Lithopop/OpenSlab/Gallery/IMG20250224133005.jpg

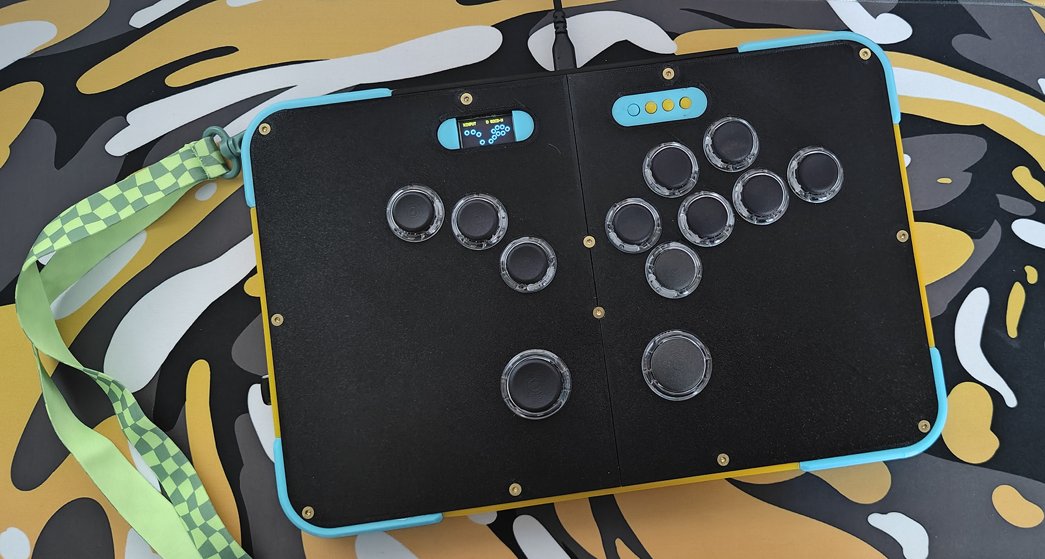
Gallery/IMG20250224133005.jpg
