Lithopop/OpenSlab/Print-Build Files/- Frame Common Files/bottom wall.stl

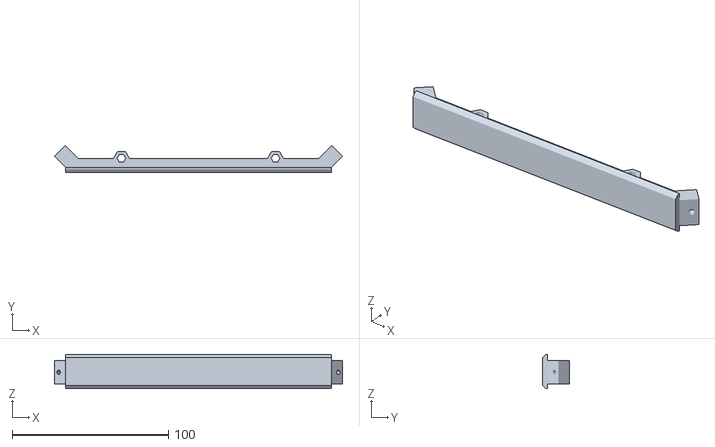
[picture p14: CAD file, 2025-02-19]
Print-Build Files/- Frame Common Files/bottom wall.stl
184.3 x 17.0 x 22.0
