Lithopop/OpenSlab/Print-Build Files/! Experimental/Acrylic Steel Plates ERGOd/Screen holder.stl

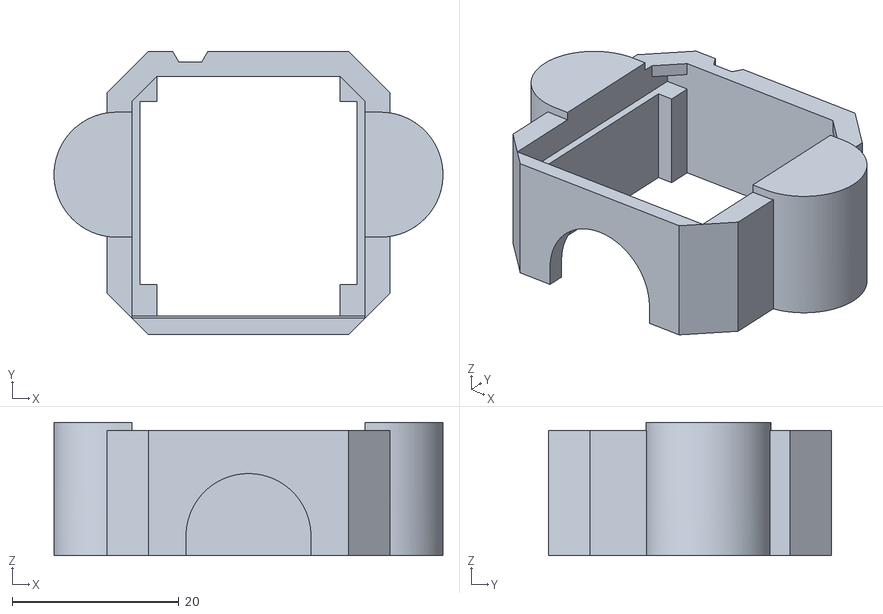
[picture p15: CAD file, 2025-02-19]
Print-Build Files/! Experimental/Acrylic Steel Plates ERGOd/Screen holder.stl
46.7 x 34.0 x 16.0
