Lithopop/OpenSlab/Print-Build Files/! Experimental/Acrylic Steel Plates ERGOd/bottom plexi.stl

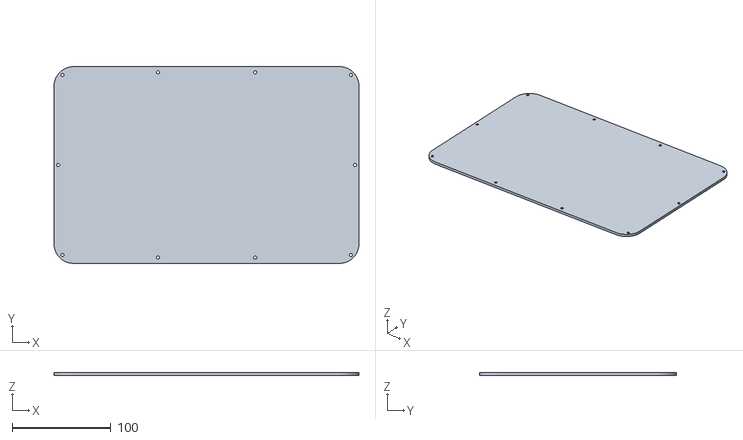
[picture p16: CAD file, 2025-02-19]
Print-Build Files/! Experimental/Acrylic Steel Plates ERGOd/bottom plexi.stl
309.4 x 199.6 x 3.00
