Lithopop/OpenSlab/Print-Build Files/- 3D Print Plates Common Files/button round 3d print.stl

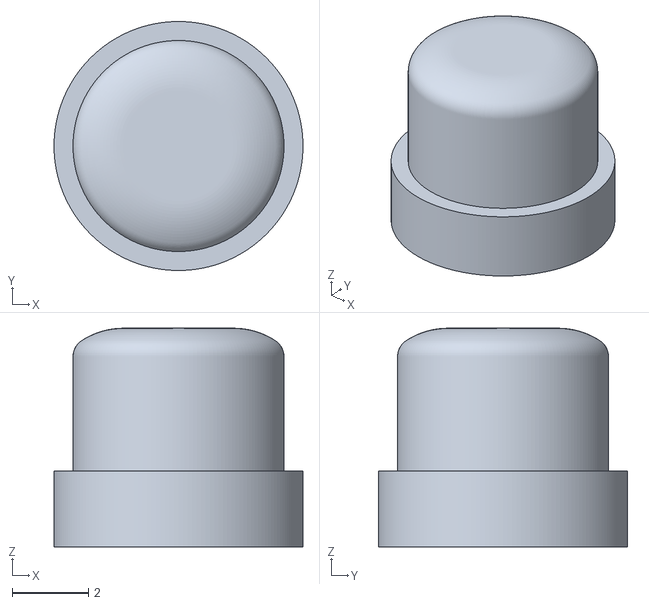
[picture p17: CAD file, 2025-02-19]
Print-Build Files/- 3D Print Plates Common Files/button round 3d print.stl
6.55 x 6.55 x 5.75
