Lithopop/OpenSlab/Print-Build Files/- Frame Common Files/Top Left.stl

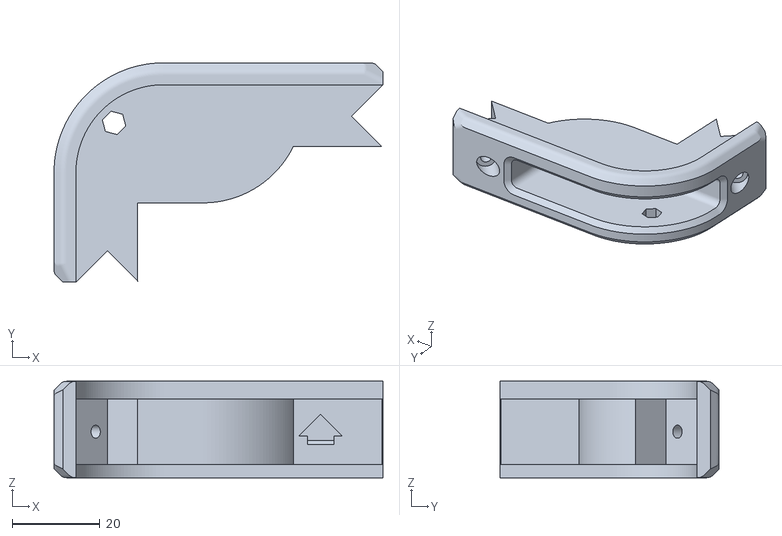
[picture p18: CAD file, 2025-02-19]
Print-Build Files/- Frame Common Files/Top Left.stl
75.0 x 50.0 x 22.0
