Lithopop/OpenSlab/Print-Build Files/! Experimental/Acrylic Steel Plates ERGOd/Steel Top.stl

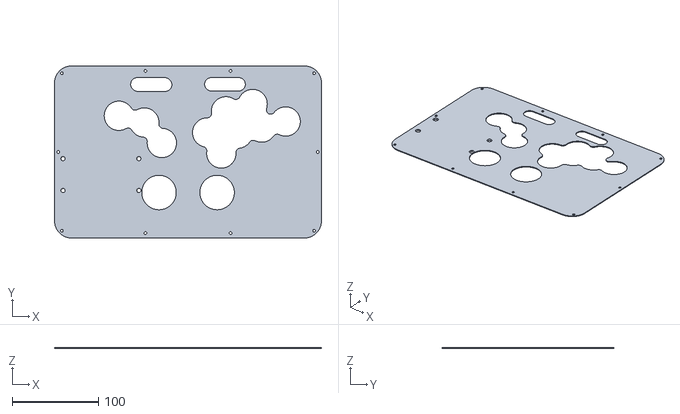
[picture p19: CAD file, 2025-02-19]
Print-Build Files/! Experimental/Acrylic Steel Plates ERGOd/Steel Top.stl
309.6 x 199.6 x 1.00
