Lithopop/OpenSlab/Print-Build Files/- 3D Print Plates Common Files/aux frame bottom.stl

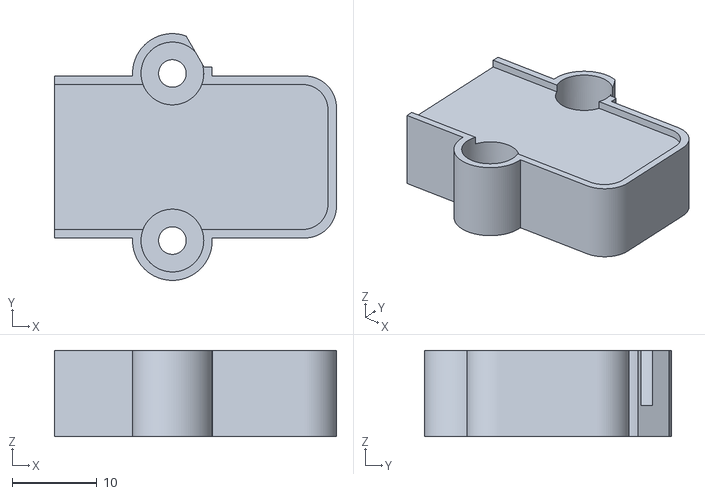
[picture p20: CAD file, 2025-02-19]
Print-Build Files/- 3D Print Plates Common Files/aux frame bottom.stl
33.2 x 29.1 x 10.2
