Lithopop/OpenSlab/Print-Build Files/! Experimental/Acrylic Steel Plates ERGOd/aux frame bottom plexi.stl

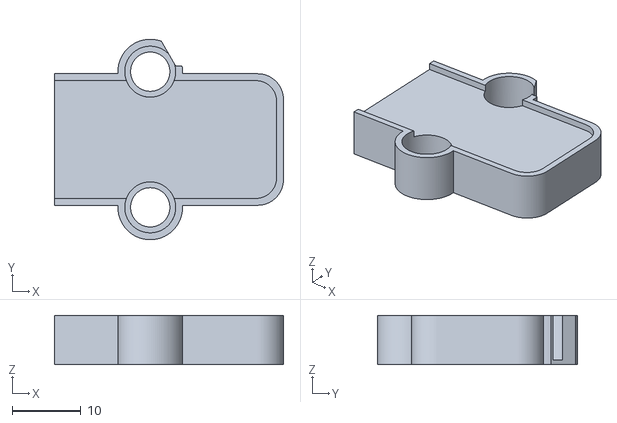
[picture p21: CAD file, 2025-02-19]
Print-Build Files/! Experimental/Acrylic Steel Plates ERGOd/aux frame bottom plexi.stl
33.2 x 29.1 x 7.15
