Lithopop/OpenSlab/Print-Build Files/- 3D Print Plates Common Files/Screen holder.stl

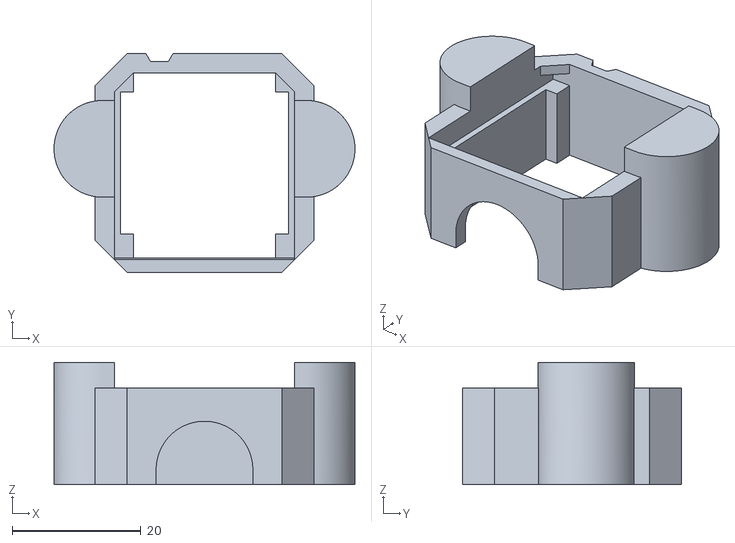
[picture p22: CAD file, 2025-02-19]
Print-Build Files/- 3D Print Plates Common Files/Screen holder.stl
46.7 x 34.0 x 19.0
