Lithopop/OpenSlab/Print-Build Files/- Frame Common Files/RP mount lid.stl

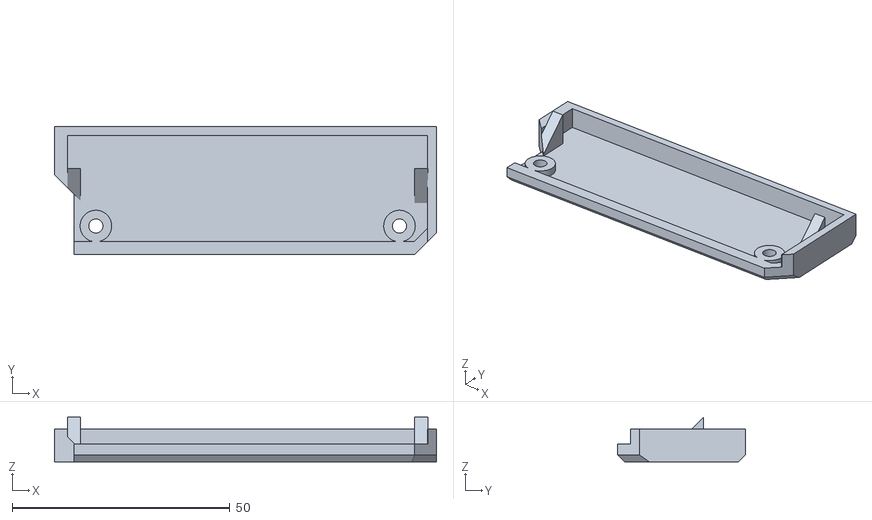
[picture p23: CAD file, 2025-02-19]
Print-Build Files/- Frame Common Files/RP mount lid.stl
87.7 x 29.3 x 10.2
