Lithopop/OpenSlab/Print-Build Files/! Experimental/Acrylic Steel Plates ERGOd/plexi Top.stl

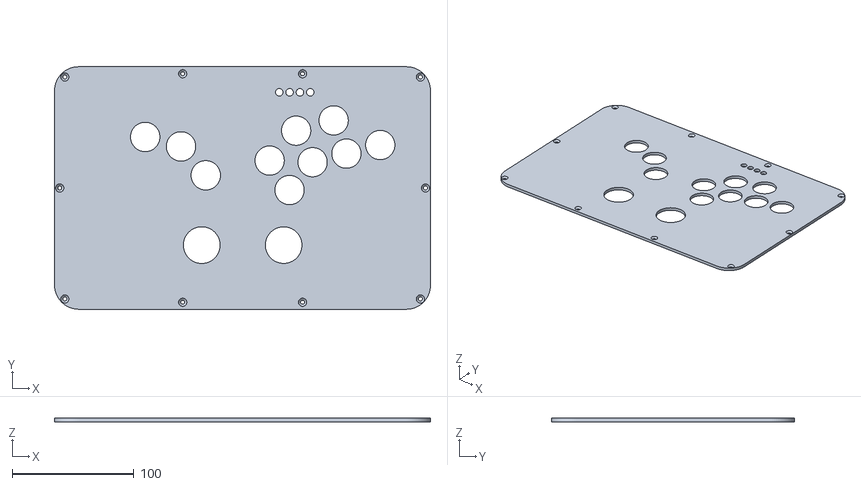
[picture p24: CAD file, 2025-02-19]
Print-Build Files/! Experimental/Acrylic Steel Plates ERGOd/plexi Top.stl
309.4 x 199.6 x 3.00
